wingprint/BatWingScanner/code/translation.py

EN = "en"
ES = "ES"

LANGUAGES = ["English", "Español"]
LANGUAGE_IDS = [EN, ES]

STRINGS = {
    "qr_id": {EN: "QR ID:\n", ES: "ID de QR:\n"},
    "disk_usage": {EN: "Disk usage:\n{} GB ({} %)", ES: "Uso del disco:\n{} GB ({} %)"},
    "external_id": {EN: "Ext. ID", ES: "ID ext."},
    "species": {EN: "Species", ES: "Especies"},
    "bag": {EN: "Bag", ES: "Bolsa"},
    "remarks": {EN: "Remarks", ES: "Observaciones"},
    "recapture": {EN: "Recapture", ES: "Recaptura"},
    "maintenance_data": {EN: "Maintenance\ndata", ES: "Datos de\nmantenimiento"},
    "save": {EN: "save", ES: "guardar"},
    "next_animal": {EN: "Next\nanimal", ES: "Siguiente\nanimal"},
    "camera": {EN: "Camera", ES: "Cámara"},
    "camera_settings": {EN: "Camera settings", ES: "Configuración de la cámara"},
    "one_photo": {EN: "Take\none picture", ES: "Toma\nuna foto"},
    "picture_sequence": {EN: "Take\npicture sequence", ES: "Toma\nsecuencia de fotos"},
    "scanning": {EN: "scanning...", ES: "escaneando..."},
    "saving_images": {EN: "saving images...", ES: "guardando imágenes..."},
    "photo_sequence": {EN: "Take\npicture sequence", ES: "Toma\nsecuencia de fotos"},
    "exposure_time": {EN: "Exposure time (s)", ES: "Tiempo de exposición (s)"},
    "gain": {EN: "Gain (dB)", ES: "Ganancia (dB)"},
    "ok": {EN: "OK", ES: "OK"},
    "cancel": {EN: "Cancel", ES: "Cancelar"},
    "duplicate_ext_id": {EN: "Duplicate external ID", ES: "ID externa duplicada"},
    "temperature": {EN: "Temperature", ES: "Temperatura"},
    "settings": {EN: "Settings", ES: "Ajustes"},
    "export": {EN: "Export", ES: "Exportar"},
    "scans": {EN: "Scans", ES: "Escaneos"},
    "select_folder": {EN: "Select folder", ES: "Seleccionar carpeta"},
    "information": {EN: "Information", ES: "Información"},
    "copying_scans": {EN: "Copying {} scans to:\n{}", ES: "Copiando {} escaneos a:\n{}"},
    "copying_finished": {EN: "Successfully copied {} scans to:\n{}", ES: "Se han copiado correctamente {} escaneos a:\n{}"}
}
